JasonThomasData/RL-arduino-bot/pics/circuit_diagram.jpg

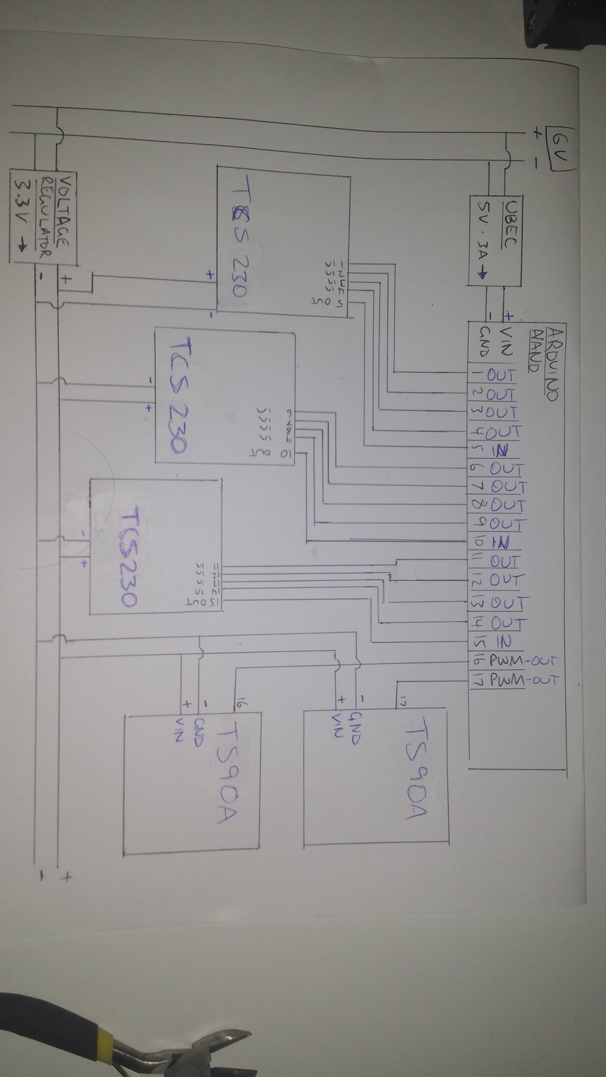
pics/circuit_diagram.jpg
