JasonThomasData/RL-arduino-bot/pics/path/tracksLayout.png

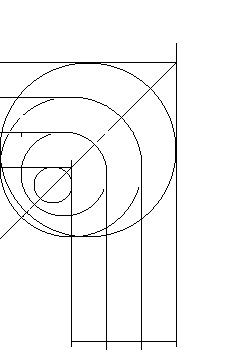
pics/path/tracksLayout.png
