JasonThomasData/RL-arduino-bot/pics/path/turn02.png

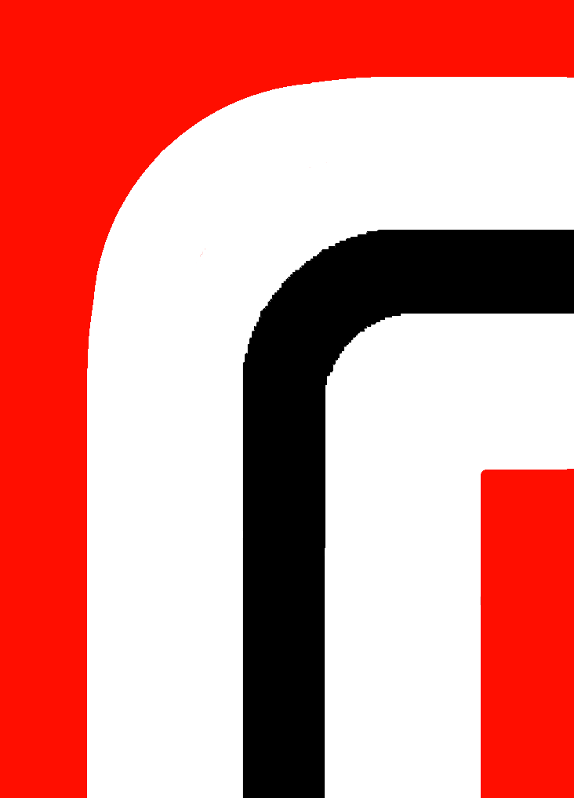
pics/path/turn02.png
