JasonThomasData/RL-arduino-bot/src/Agent/StateActionPairs.h

#ifndef State_h
#define State_h
struct State
{
    char sensorLeft;
    char sensorMiddle;
    char sensorRight;
    char memoryKey[3];
};
#endif

#ifndef Action_h
#define Action_h
struct Action
{
    int leftWheelDirection;
    int rightWheelDirection;
    char memoryKey[2];
};
#endif

#ifndef StateActionPair_h
#define StateActionPair_h
struct StateActionPair
{
    State state;
    Action action;
};
#endif
