JasonThomasData/RL-arduino-bot/src/Agent/Models.h

#ifndef SensorModel_h
#define SensorModel_h
struct SensorModel
{
    int s2Pin;
    int s3Pin;
    int outputPin;
};
#endif

#ifndef ServoModel_h
#define ServoModel_h
struct ServoModel
{
    int pin;
    int moveDuration;
};
#endif
